DotaPie/Dakboard-HDMI-dimmer-HW/Dakboard-HDMI-dimmer-HW-KiCAD/Mainboard v1/Mainboard v1.kicad_sch

## KiCad design Dakboard-HDMI-dimmer-HW-KiCAD/Mainboard v1/Mainboard v1.kicad_sch (2026-05-16)

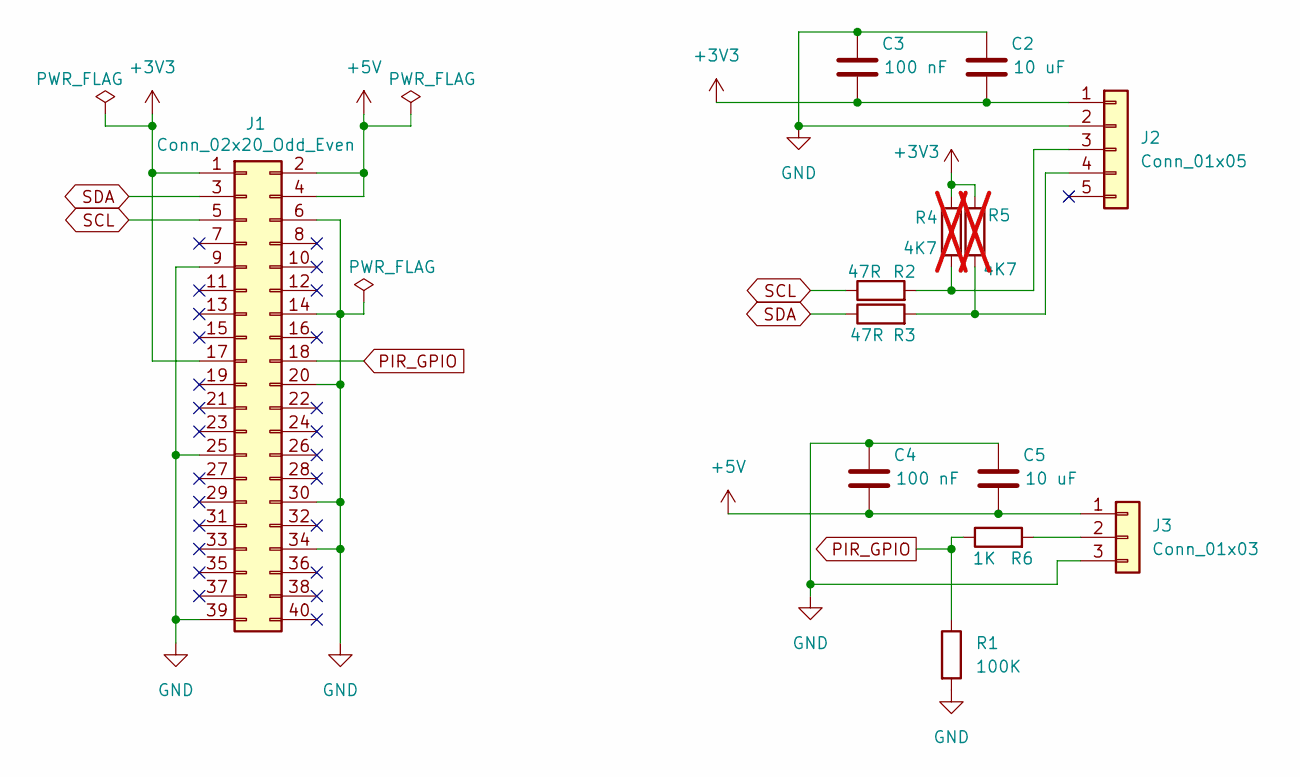
[picture p4: schematic Mainboard v1.kicad_sch]

Parts:
C2, C5: 10 uF; C_0805_2012Metric_Pad1.18x1.45mm_HandSolder
C3, C4: 100 nF; C_0805_2012Metric_Pad1.18x1.45mm_HandSolder
J1: Conn_02x20_Odd_Even; PinSocket_2x20_P2.54mm_Vertical
J2: Conn_01x05; PinHeader_1x05_P2.54mm_Horizontal
J3: Conn_01x03; PinHeader_1x03_P2.54mm_Horizontal
R1: 100K; R_0805_2012Metric_Pad1.20x1.40mm_HandSolder
R2, R3: 47R; R_0805_2012Metric_Pad1.20x1.40mm_HandSolder
R4, R5: 4K7; R_0805_2012Metric_Pad1.20x1.40mm_HandSolder; not fitted
R6: 1K; R_0805_2012Metric_Pad1.20x1.40mm_HandSolder

Connections:
+3V3: C2.2, C3.2, J1.1, J1.17, J2.1, R4.1, R5.1
+5V: C4.2, C5.2, J1.2, J1.4, J3.1
GND: C2.1, C3.1, C4.1, C5.1, J1.6, J1.9, J1.14, J1.20, J1.25, J1.30, J1.34, J1.39, J2.2, J3.3, R1.2
unnamed: J2.3, R2.2, R4.2
unnamed: J2.4, R3.2, R5.2
unnamed: J3.2, R6.2
PIR_GPIO: J1.18, R1.1, R6.1
SCL: J1.5, R2.1
SDA: J1.3, R3.1
